JJong2542/Mini-Z-Universal-Dummy-Frame-Adjustable/Drawings/Legacy_1.2/F01-0005-02_Post.pdf

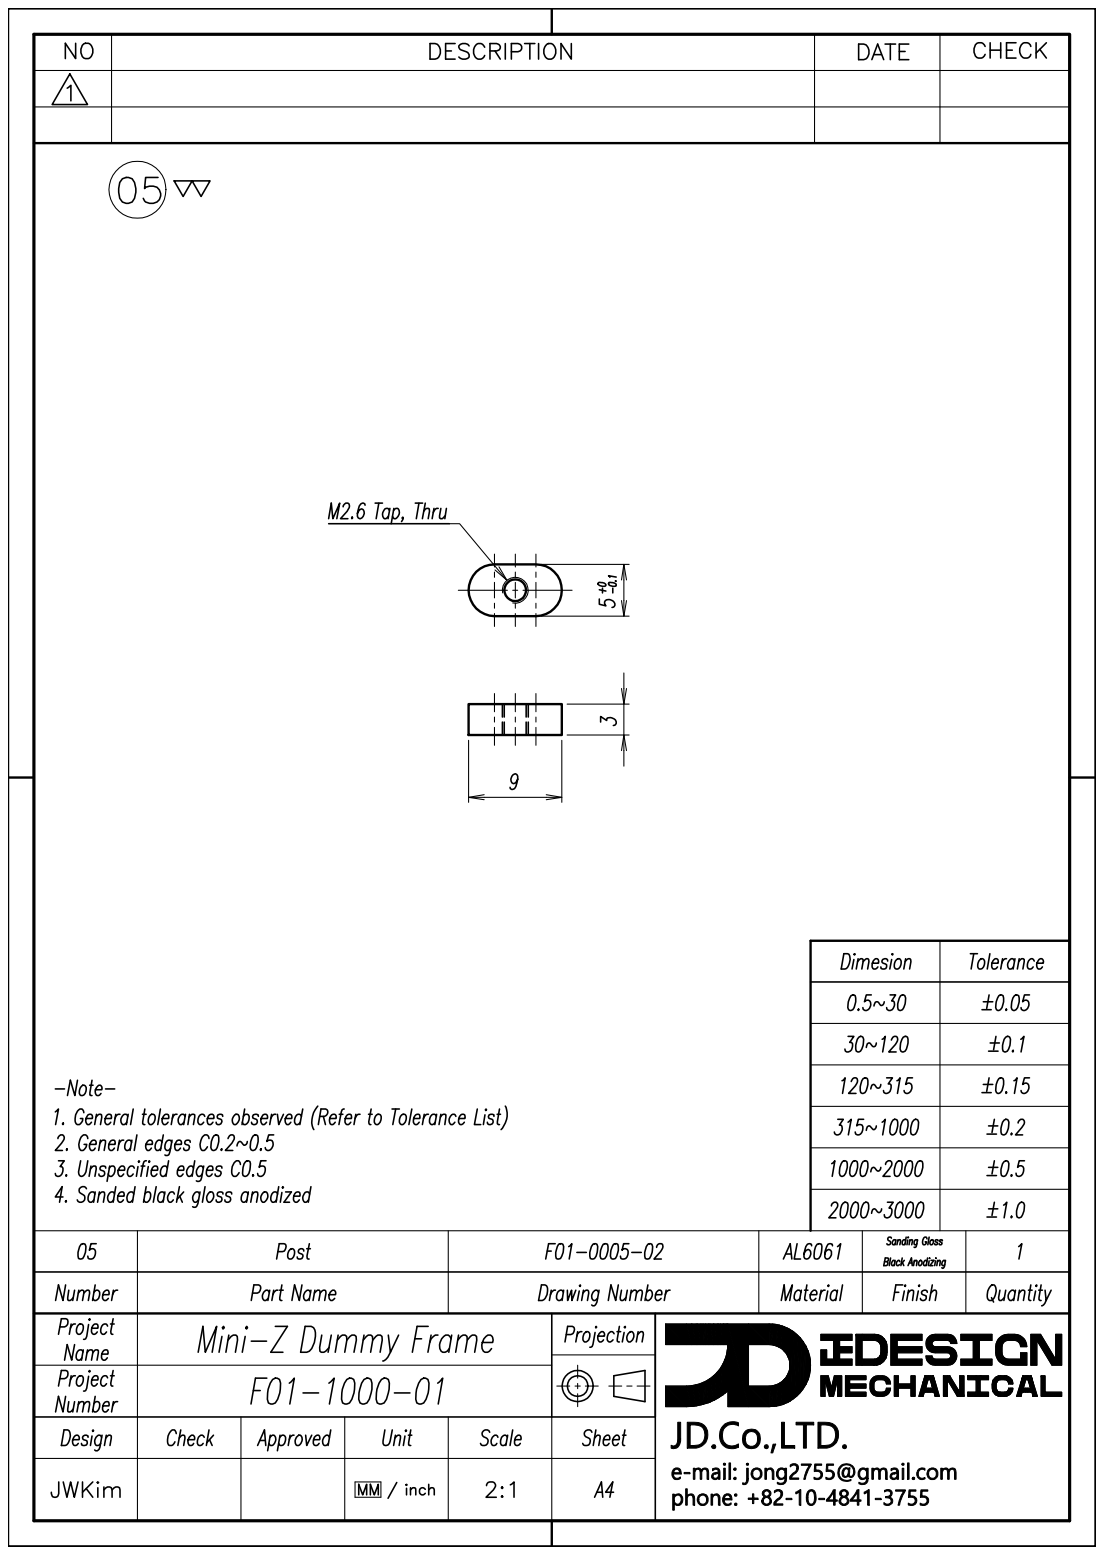
[picture p33: page 1]
