JJong2542/Mini-Z-Universal-Dummy-Frame-Adjustable/Drawings/Legacy_1.2/F01-0006-01-Mount Case Block.pdf

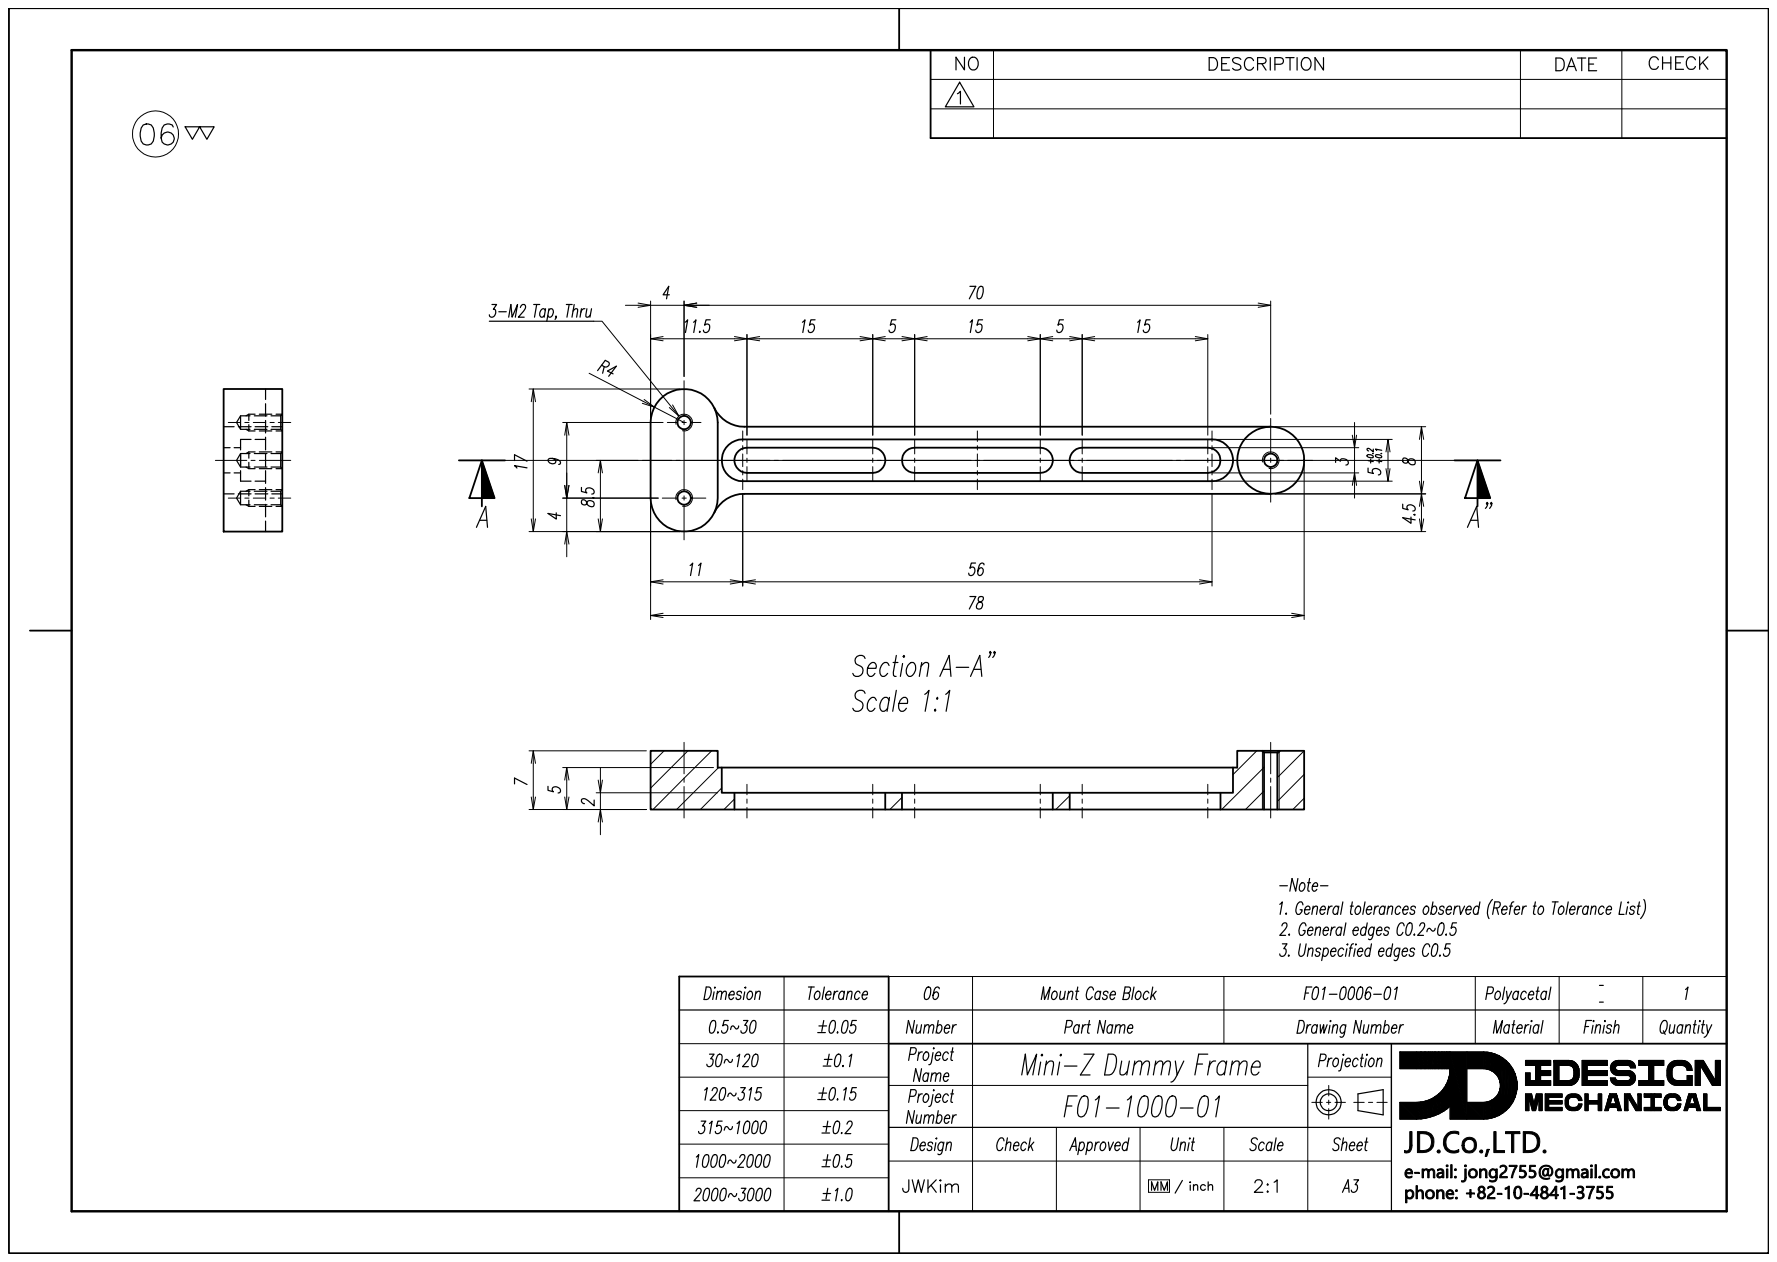
[picture p34: page 1]
